null-ll/pinstripe/pcb/pinstripe/pinstripe.kicad_sch

## KiCad design pcb/pinstripe/pinstripe.kicad_sch (2023-01-03)

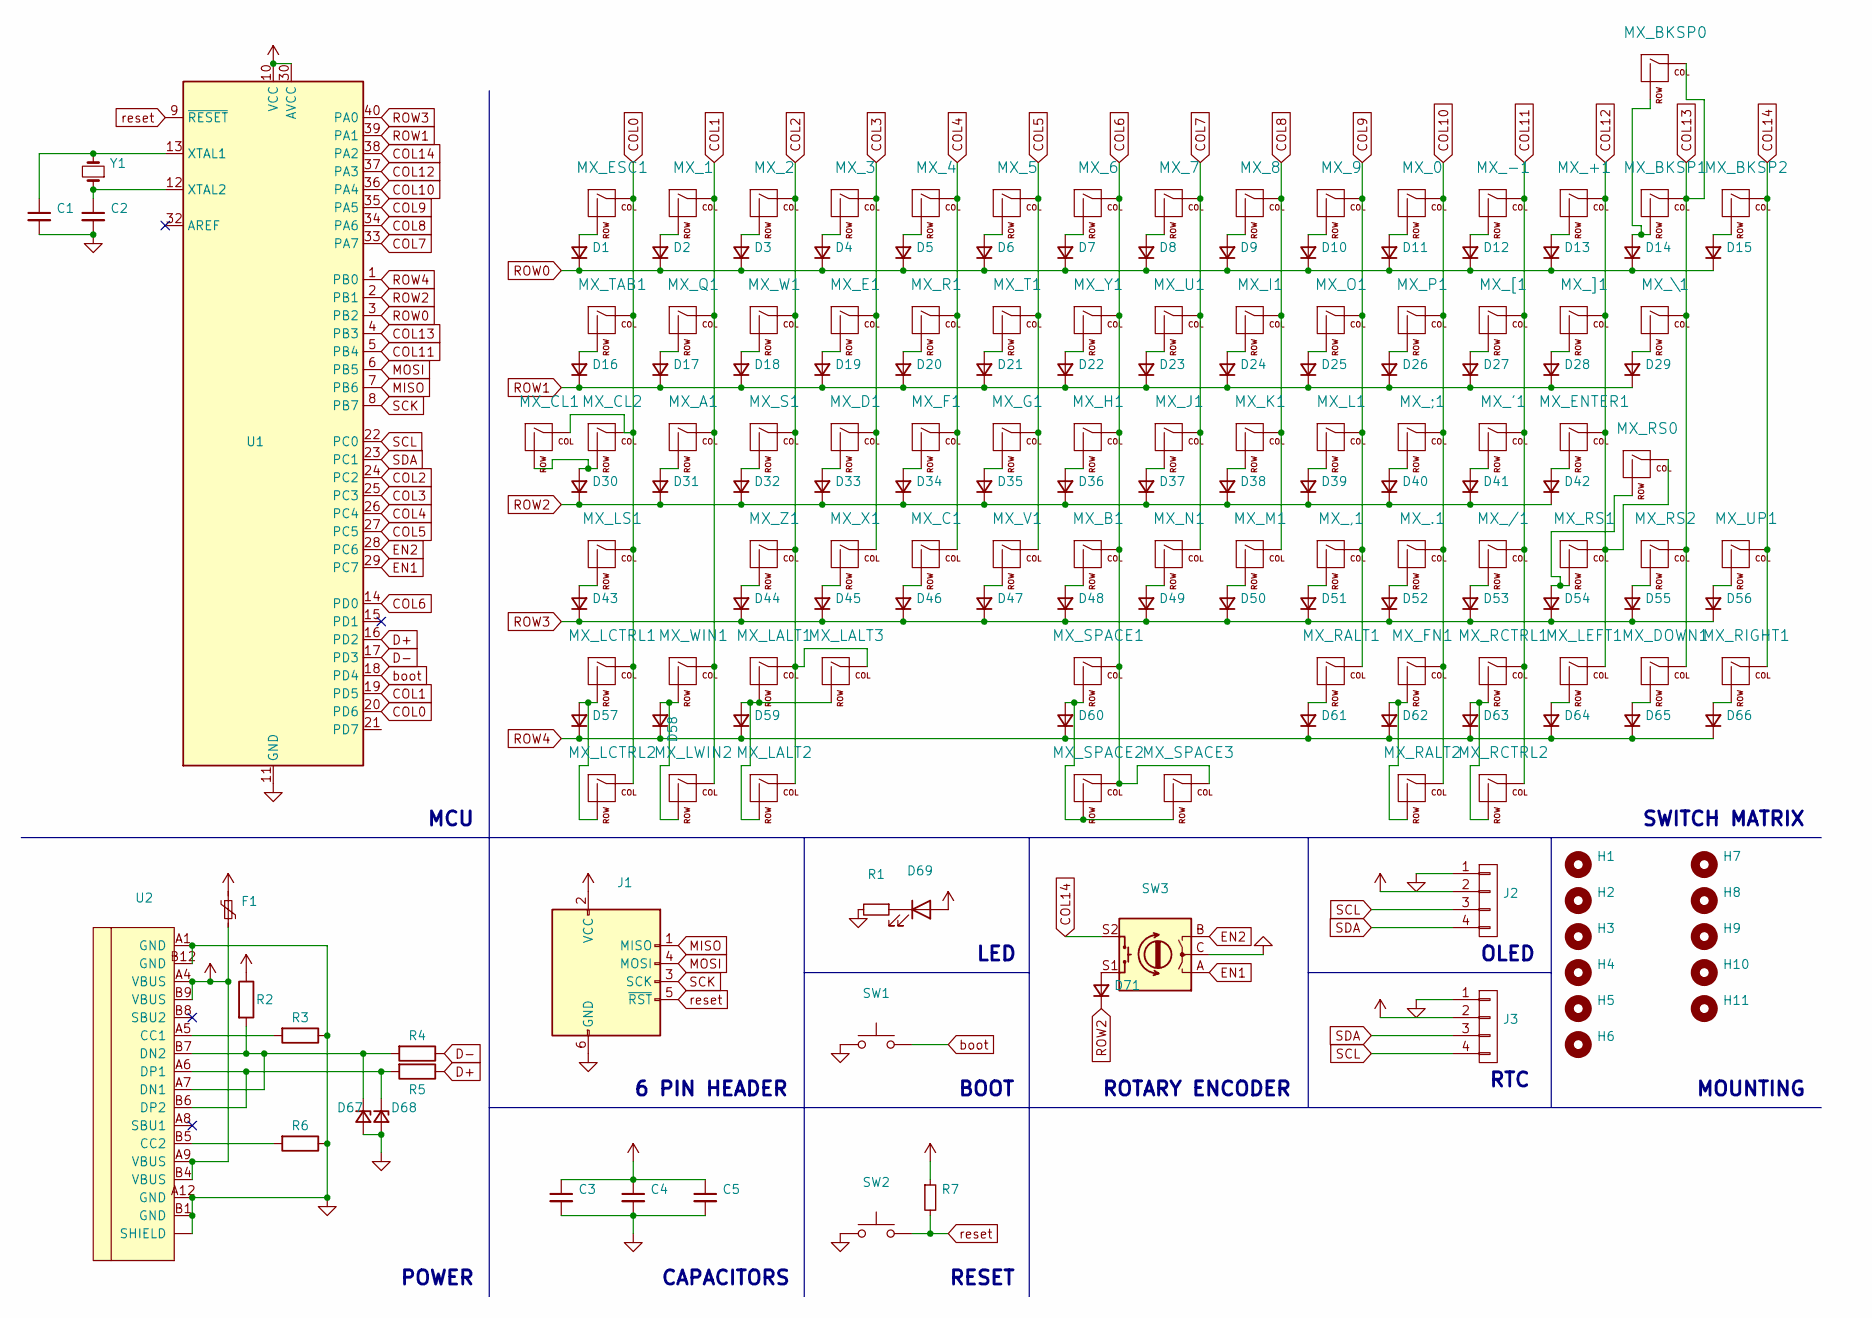
[picture p4: schematic pinstripe.kicad_sch]

Parts:
C1, C2, C3, C4, C5: (no value)
D1, D2, D3, D4, D5, D6, D7, D8, D9, D10, D11, D12, D13, D14, D15, D16, D17, D18, D19, D20, D21, D22, D23, D24, D25, D26, D27, D28, D29, D30, D31, D32, D33, D34, D35, D36, D37, D38, D39, D40, D41, D42, D43, D44, D45, D46, D47, D48, D49, D50, D51, D52, D53, D54, D55, D56, D57, D58, D59, D60, D61, D62, D63, D64, D65, D66, D67, D68, D69, D71: (no value)
F1: (no value)
H1, H2, H3, H4, H5, H6, H7, H8, H9, H10, H11: (no value)
J1, J2, J3: (no value)
MX_0, MX_1, MX_2, MX_3, MX_4, MX_5, MX_6, MX_7, MX_8, MX_9, MX_.1: (no value)
MX_'1: (no value)
MX_+1: (no value)
MX_,1: (no value)
MX_-1: (no value)
MX_/1: (no value)
MX_;1: (no value)
MX_A1: (no value)
MX_B1: (no value)
MX_BKSP0, MX_BKSP1, MX_BKSP2: (no value)
MX_C1: (no value)
MX_CL1, MX_CL2: (no value)
MX_D1: (no value)
MX_DOWN1: (no value)
MX_E1: (no value)
MX_ENTER1: (no value)
MX_ESC1: (no value)
MX_F1: (no value)
MX_FN1: (no value)
MX_G1: (no value)
MX_H1: (no value)
MX_I1: (no value)
MX_J1: (no value)
MX_K1: (no value)
MX_L1: (no value)
MX_LALT1, MX_LALT2, MX_LALT3: (no value)
MX_LCTRL1, MX_LCTRL2: (no value)
MX_LEFT1: (no value)
MX_LS1: (no value)
MX_LWIN2: (no value)
MX_M1: (no value)
MX_N1: (no value)
MX_O1: (no value)
MX_P1: (no value)
MX_Q1: (no value)
MX_R1: (no value)
MX_RALT1, MX_RALT2: (no value)
MX_RCTRL1, MX_RCTRL2: (no value)
MX_RIGHT1: (no value)
MX_RS0, MX_RS1, MX_RS2: (no value)
MX_S1: (no value)
MX_SPACE1, MX_SPACE2, MX_SPACE3: (no value)
MX_T1: (no value)
MX_TAB1: (no value)
MX_U1: (no value)
MX_UP1: (no value)
MX_V1: (no value)
MX_W1: (no value)
MX_WIN1: (no value)
MX_X1: (no value)
MX_Y1: (no value)
MX_Z1: (no value)
MX_[1: (no value)
MX_\1: (no value)
MX_]1: (no value)
R1, R2, R3, R4, R5, R6, R7: (no value)
SW1, SW2, SW3: (no value)
U1, U2: (no value)
Y1: (no value)

Connections:
COL0: MX_CL1.1 (COL), MX_CL2.1 (COL), MX_ESC1.1 (COL), MX_LCTRL1.1 (COL), MX_LCTRL2.1 (COL), MX_LS1.1 (COL), MX_TAB1.1 (COL), U1.20 (PD6)
COL1: MX_1.1 (COL), MX_A1.1 (COL), MX_LWIN2.1 (COL), MX_Q1.1 (COL), MX_WIN1.1 (COL), U1.19 (PD5)
COL2: MX_2.1 (COL), MX_LALT1.1 (COL), MX_LALT2.1 (COL), MX_LALT3.1 (COL), MX_S1.1 (COL), MX_W1.1 (COL), MX_Z1.1 (COL), U1.24 (PC2)
COL3: MX_3.1 (COL), MX_D1.1 (COL), MX_E1.1 (COL), MX_X1.1 (COL), U1.25 (PC3)
COL4: MX_4.1 (COL), MX_C1.1 (COL), MX_F1.1 (COL), MX_R1.1 (COL), U1.26 (PC4)
COL5: MX_5.1 (COL), MX_G1.1 (COL), MX_T1.1 (COL), MX_V1.1 (COL), U1.27 (PC5)
COL6: MX_6.1 (COL), MX_B1.1 (COL), MX_H1.1 (COL), MX_SPACE1.1 (COL), MX_SPACE2.1 (COL), MX_SPACE3.1 (COL), MX_Y1.1 (COL), U1.14 (PD0)
COL7: MX_7.1 (COL), MX_J1.1 (COL), MX_N1.1 (COL), MX_U1.1 (COL), U1.33 (PA7)
COL8: MX_8.1 (COL), MX_I1.1 (COL), MX_K1.1 (COL), MX_M1.1 (COL), U1.34 (PA6)
COL9: MX_9.1 (COL), MX_,1.1 (COL), MX_L1.1 (COL), MX_O1.1 (COL), MX_RALT1.1 (COL), U1.35 (PA5)
COL10: MX_0.1 (COL), MX_.1.1 (COL), MX_;1.1 (COL), MX_FN1.1 (COL), MX_P1.1 (COL), MX_RALT2.1 (COL), U1.36 (PA4)
COL11: MX_'1.1 (COL), MX_-1.1 (COL), MX_/1.1 (COL), MX_RCTRL1.1 (COL), MX_RCTRL2.1 (COL), MX_[1.1 (COL), U1.5 (PB4)
COL12: MX_+1.1 (COL), MX_ENTER1.1 (COL), MX_LEFT1.1 (COL), MX_RS0.1 (COL), MX_RS1.1 (COL), MX_]1.1 (COL), U1.37 (PA3)
COL13: MX_BKSP0.1 (COL), MX_BKSP1.1 (COL), MX_DOWN1.1 (COL), MX_RS2.1 (COL), MX_\1.1 (COL), U1.4 (PB3)
COL14: MX_BKSP2.1 (COL), MX_RIGHT1.1 (COL), MX_UP1.1 (COL), SW3.S2, U1.38 (PA2)
D+: R5.1, U1.16 (PD2)
D-: R4.1, U1.17 (PD3)
EN1: SW3.A, U1.29 (PC7)
EN2: SW3.B, U1.28 (PC6)
MISO: J1.1 (MISO), U1.7 (PB6)
MOSI: J1.4 (MOSI), U1.6 (PB5)
unnamed: C1.1, U1.13 (XTAL1), Y1.2
unnamed: C1.2, C2.2, C3.1, C3.2, C4.1, C4.2, C5.1, C5.2, D67.2 (A), D68.2 (A), D69.2 (A), F1.1, F1.2, J1.2 (VCC), J1.6 (GND), J2.1, J2.2, J3.1, J3.2, R1.2, R2.1, R3.1, R6.1, R7.1, SW1.1, SW2.1, SW3.C, U1.10 (VCC), U1.11 (GND), U1.30 (AVCC), U1.31 (GND), U2.A1 (GND), U2.A4 (VBUS), U2.A9 (VBUS), U2.A12 (GND), U2.B1 (GND), U2.B4 (VBUS), U2.B9 (VBUS), U2.B12 (GND), U2.~ (SHIELD)
unnamed: C2.1, U1.12 (XTAL2), Y1.1
unnamed: D1.2 (A), MX_ESC1.2 (ROW)
unnamed: D2.2 (A), MX_1.2 (ROW)
unnamed: D3.2 (A), MX_2.2 (ROW)
unnamed: D4.2 (A), MX_3.2 (ROW)
unnamed: D5.2 (A), MX_4.2 (ROW)
unnamed: D6.2 (A), MX_5.2 (ROW)
unnamed: D7.2 (A), MX_6.2 (ROW)
unnamed: D8.2 (A), MX_7.2 (ROW)
unnamed: D9.2 (A), MX_8.2 (ROW)
unnamed: D10.2 (A), MX_9.2 (ROW)
unnamed: D11.2 (A), MX_0.2 (ROW)
unnamed: D12.2 (A), MX_-1.2 (ROW)
unnamed: D13.2 (A), MX_+1.2 (ROW)
unnamed: D14.2 (A), MX_BKSP0.2 (ROW), MX_BKSP1.2 (ROW)
unnamed: D15.2 (A), MX_BKSP2.2 (ROW)
unnamed: D16.2 (A), MX_TAB1.2 (ROW)
unnamed: D17.2 (A), MX_Q1.2 (ROW)
unnamed: D18.2 (A), MX_W1.2 (ROW)
unnamed: D19.2 (A), MX_E1.2 (ROW)
unnamed: D20.2 (A), MX_R1.2 (ROW)
unnamed: D21.2 (A), MX_T1.2 (ROW)
unnamed: D22.2 (A), MX_Y1.2 (ROW)
unnamed: D23.2 (A), MX_U1.2 (ROW)
unnamed: D24.2 (A), MX_I1.2 (ROW)
unnamed: D25.2 (A), MX_O1.2 (ROW)
unnamed: D26.2 (A), MX_P1.2 (ROW)
unnamed: D27.2 (A), MX_[1.2 (ROW)
unnamed: D28.2 (A), MX_]1.2 (ROW)
unnamed: D29.2 (A), MX_\1.2 (ROW)
unnamed: D30.2 (A), MX_CL1.2 (ROW), MX_CL2.2 (ROW)
unnamed: D31.2 (A), MX_A1.2 (ROW)
unnamed: D32.2 (A), MX_S1.2 (ROW)
unnamed: D33.2 (A), MX_D1.2 (ROW)
unnamed: D34.2 (A), MX_F1.2 (ROW)
unnamed: D35.2 (A), MX_G1.2 (ROW)
unnamed: D36.2 (A), MX_H1.2 (ROW)
unnamed: D37.2 (A), MX_J1.2 (ROW)
unnamed: D38.2 (A), MX_K1.2 (ROW)
unnamed: D39.2 (A), MX_L1.2 (ROW)
unnamed: D40.2 (A), MX_;1.2 (ROW)
unnamed: D41.2 (A), MX_'1.2 (ROW)
unnamed: D42.2 (A), MX_ENTER1.2 (ROW)
unnamed: D43.2 (A), MX_LS1.2 (ROW)
unnamed: D44.2 (A), MX_Z1.2 (ROW)
unnamed: D45.2 (A), MX_X1.2 (ROW)
unnamed: D46.2 (A), MX_C1.2 (ROW)
unnamed: D47.2 (A), MX_V1.2 (ROW)
unnamed: D48.2 (A), MX_B1.2 (ROW)
unnamed: D49.2 (A), MX_N1.2 (ROW)
unnamed: D50.2 (A), MX_M1.2 (ROW)
unnamed: D51.2 (A), MX_,1.2 (ROW)
unnamed: D52.2 (A), MX_.1.2 (ROW)
unnamed: D53.2 (A), MX_/1.2 (ROW)
unnamed: D54.2 (A), MX_RS0.2 (ROW), MX_RS1.2 (ROW)
unnamed: D55.2 (A), MX_RS2.2 (ROW)
unnamed: D56.2 (A), MX_UP1.2 (ROW)
unnamed: D57.2 (A), MX_LCTRL1.2 (ROW), MX_LCTRL2.2 (ROW)
unnamed: D58.2 (A), MX_LWIN2.2 (ROW), MX_WIN1.2 (ROW)
unnamed: D59.2 (A), MX_LALT1.2 (ROW), MX_LALT2.2 (ROW), MX_LALT3.2 (ROW)
unnamed: D60.2 (A), MX_SPACE1.2 (ROW), MX_SPACE2.2 (ROW), MX_SPACE3.2 (ROW)
unnamed: D61.2 (A), MX_RALT1.2 (ROW)
unnamed: D62.2 (A), MX_FN1.2 (ROW), MX_RALT2.2 (ROW)
unnamed: D63.2 (A), MX_RCTRL1.2 (ROW), MX_RCTRL2.2 (ROW)
unnamed: D64.2 (A), MX_LEFT1.2 (ROW)
unnamed: D65.2 (A), MX_DOWN1.2 (ROW)
unnamed: D66.2 (A), MX_RIGHT1.2 (ROW)
unnamed: D67.1 (K), R2.2, R4.2, U2.A7 (DN1), U2.B7 (DN2)
unnamed: D68.1 (K), R5.2, U2.A6 (DP1), U2.B6 (DP2)
unnamed: D69.1 (K), R1.1
unnamed: D71.2 (A), SW3.S1
unnamed: R3.2, U2.A5 (CC1)
unnamed: R6.2, U2.B5 (CC2)
ROW0: D1.1 (K), D2.1 (K), D3.1 (K), D4.1 (K), D5.1 (K), D6.1 (K), D7.1 (K), D8.1 (K), D9.1 (K), D10.1 (K), D11.1 (K), D12.1 (K), D13.1 (K), D14.1 (K), D15.1 (K), U1.3 (PB2)
ROW1: D16.1 (K), D17.1 (K), D18.1 (K), D19.1 (K), D20.1 (K), D21.1 (K), D22.1 (K), D23.1 (K), D24.1 (K), D25.1 (K), D26.1 (K), D27.1 (K), D28.1 (K), D29.1 (K), U1.39 (PA1)
ROW2: D30.1 (K), D31.1 (K), D32.1 (K), D33.1 (K), D34.1 (K), D35.1 (K), D36.1 (K), D37.1 (K), D38.1 (K), D39.1 (K), D40.1 (K), D41.1 (K), D42.1 (K), D71.1 (K), U1.2 (PB1)
ROW3: D43.1 (K), D44.1 (K), D45.1 (K), D46.1 (K), D47.1 (K), D48.1 (K), D49.1 (K), D50.1 (K), D51.1 (K), D52.1 (K), D53.1 (K), D54.1 (K), D55.1 (K), D56.1 (K), U1.40 (PA0)
ROW4: D57.1 (K), D58.1 (K), D59.1 (K), D60.1 (K), D61.1 (K), D62.1 (K), D63.1 (K), D64.1 (K), D65.1 (K), D66.1 (K), U1.1 (PB0)
SCK: J1.3 (SCK), U1.8 (PB7)
SCL: J2.3, J3.4, U1.22 (PC0)
SDA: J2.4, J3.3, U1.23 (PC1)
boot: SW1.2, U1.18 (PD4)
reset: J1.5 (~RST), R7.2, SW2.2, U1.9 (~RESET)

Notes on the sheet:
SWITCH MATRIX
BOOT
ROTARY ENCODER
RTC
MCU
CAPACITORS
6 PIN HEADER
MOUNTING
POWER
OLED
LED
RESET
